uscmakers/the-pipeline/klipper/printer_data/config/custom/speed-limits-performance.cfg

[printer]
max_velocity: 200
max_accel: 5000
max_accel_to_decel: 5000
max_z_velocity: 15
max_z_accel: 100
square_corner_velocity: 5

[bed_mesh]
speed: 200

[z_tilt]
speed: 200

[manual_stepper stepper_pusha]
velocity: 50
accel: 200
