uscmakers/the-pipeline/klipper/printer_data/config/custom/aero.cfg

[extruder]
rotation_distance: 7.644542
filament_diameter: 2.85
full_steps_per_rotation: 200
max_extrude_only_velocity: 50

[extruder1]
rotation_distance: 7.644542
filament_diameter: 2.85
full_steps_per_rotation: 200
max_extrude_only_velocity: 50

[firmware_retraction]
retract_speed: 40
unretract_extra_length: 0
unretract_speed: 40
